santiagocuenta112az-lgtm/glamrock-freddy/mano/mano.stl

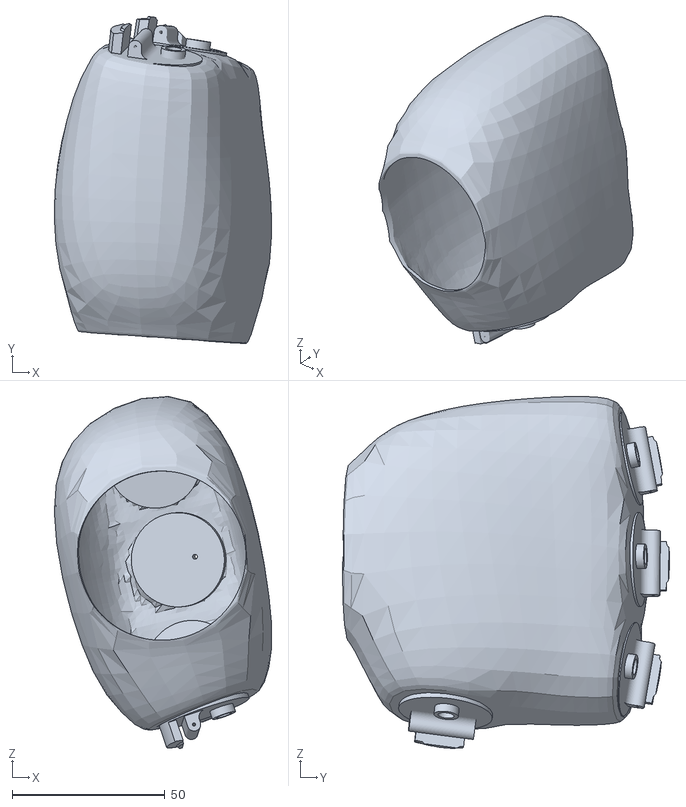
[picture p15: CAD file, 2026-02-24]
mano/mano.stl
71.1 x 107.0 x 115.2
