santiagocuenta112az-lgtm/glamrock-freddy/mis mecanismos/brazo/planetas.stl

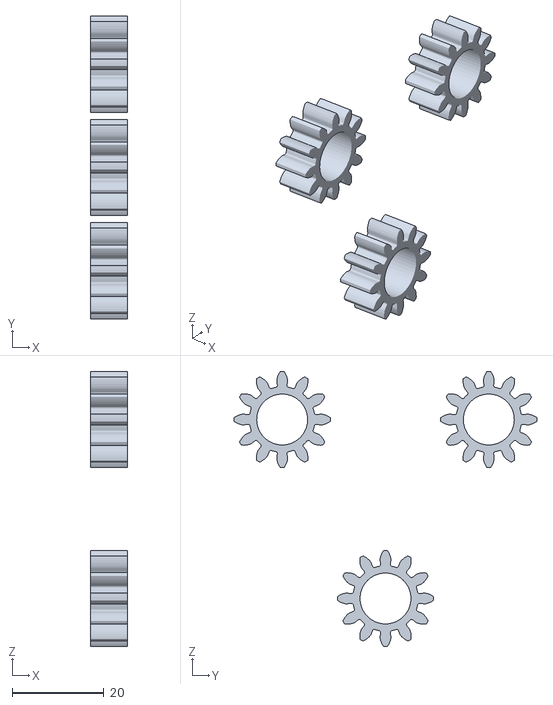
[picture p16: CAD file, 2026-02-24]
mis mecanismos/brazo/planetas.stl
8.00 x 66.0 x 60.0
