santiagocuenta112az-lgtm/glamrock-freddy/mis mecanismos/mecanismo de placa alta/3.stl

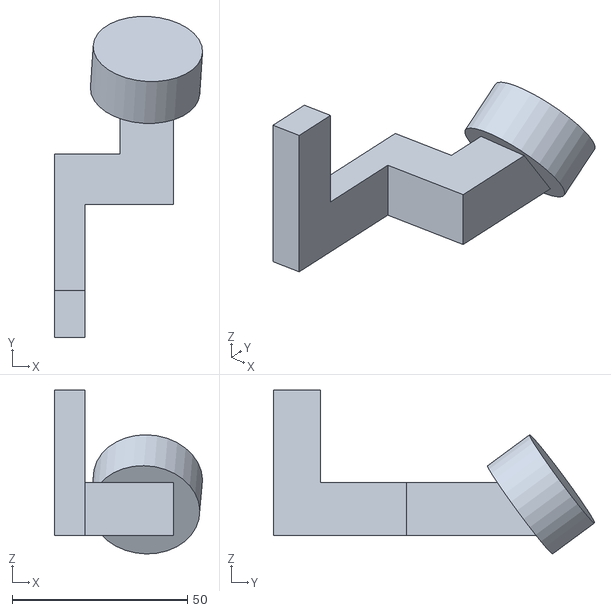
[picture p17: CAD file, 2026-02-24]
mis mecanismos/mecanismo de placa alta/3.stl
42.3 x 91.7 x 46.8
