santiagocuenta112az-lgtm/glamrock-freddy/mis mecanismos/mecanismo giro pecho/2.stl

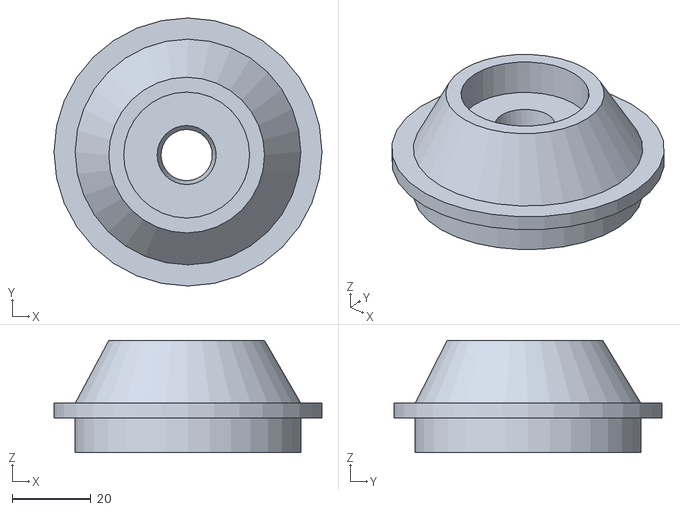
[picture p18: CAD file, 2026-02-24]
mis mecanismos/mecanismo giro pecho/2.stl
68.1 x 68.1 x 28.5
