santiagocuenta112az-lgtm/glamrock-freddy/mis mecanismos/mecanismo placa baja/base del motor.stl

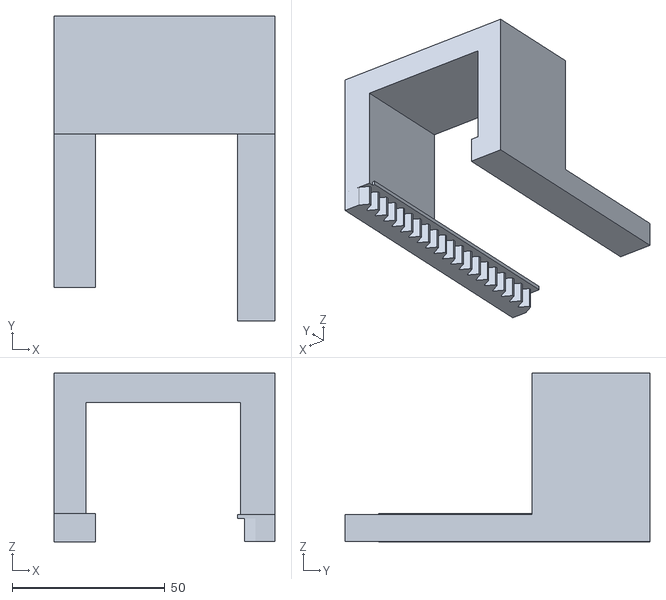
[picture p19: CAD file, 2026-06-25]
mis mecanismos/mecanismo placa baja/base del motor.stl
72.4 x 99.8 x 55.2
