santiagocuenta112az-lgtm/glamrock-freddy/mis mecanismos/soportes/conexioncuellocabeza.stl

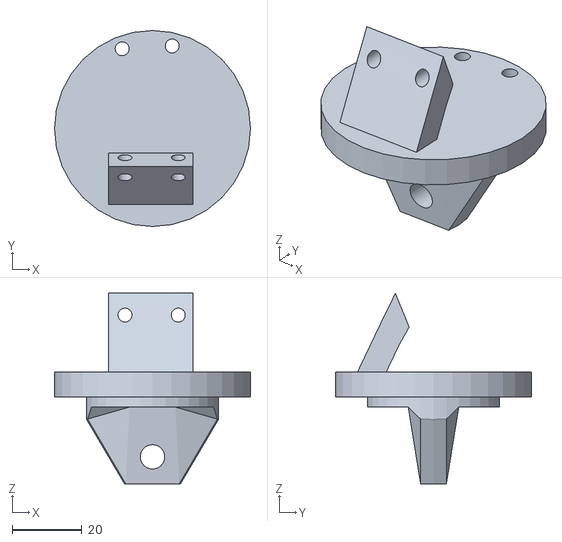
[picture p20: CAD file, 2026-02-24]
mis mecanismos/soportes/conexioncuellocabeza.stl
56.3 x 56.3 x 54.8
