santiagocuenta112az-lgtm/glamrock-freddy/ojos/pestaña.stl

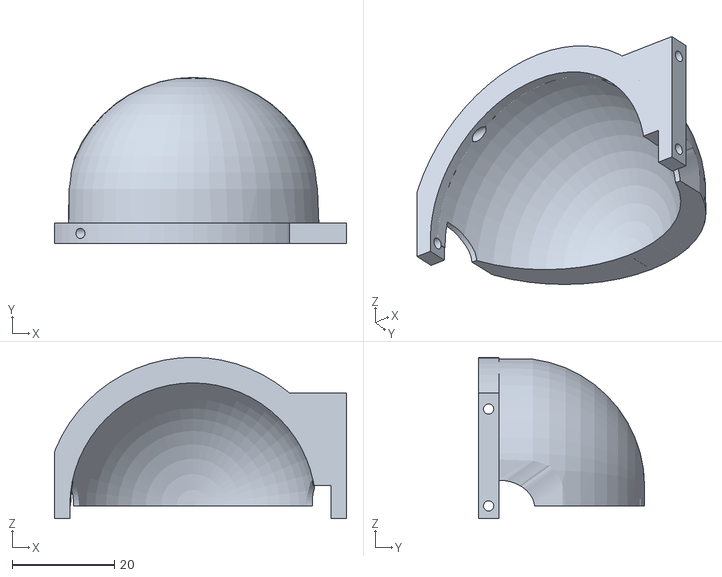
[picture p21: CAD file, 2026-02-24]
ojos/pestaña.stl
57.0 x 32.4 x 31.5
