santiagocuenta112az-lgtm/glamrock-freddy/planetary gearbox.3mf

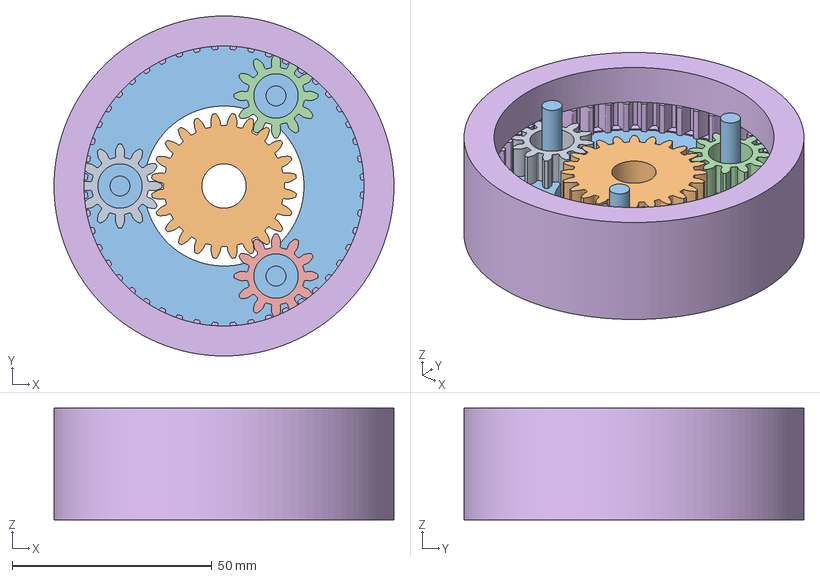
[picture p22: CAD file, 2026-02-24]
planetary gearbox.3mf
85.0 x 85.0 x 28.0 mm
Cuerpo1 x 3
Cuerpo2
Cuerpo3
Cuerpo5
