santiagocuenta112az-lgtm/glamrock-freddy/cara/oreja 2.stl

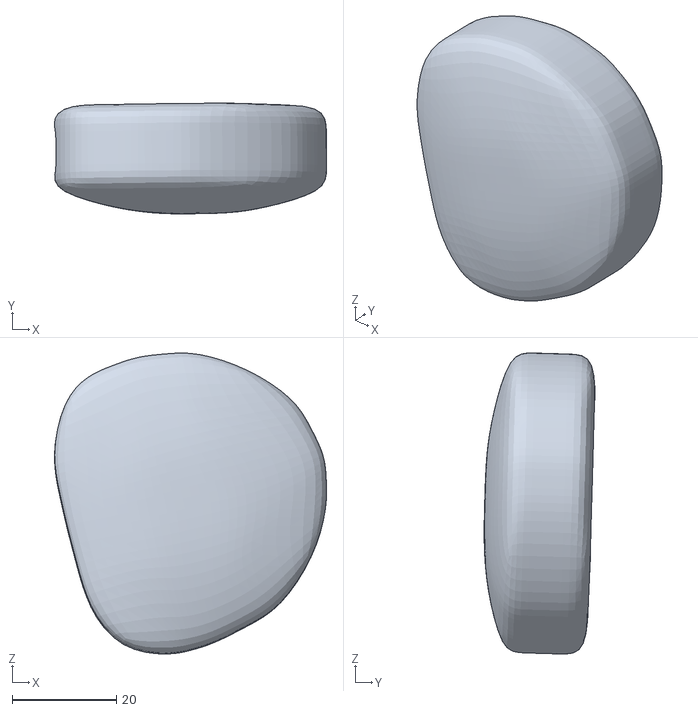
[picture p23: CAD file, 2026-02-24]
cara/oreja 2.stl
52.1 x 21.2 x 57.7
