santiagocuenta112az-lgtm/glamrock-freddy/cuerpo/extremidades/brazo.stl

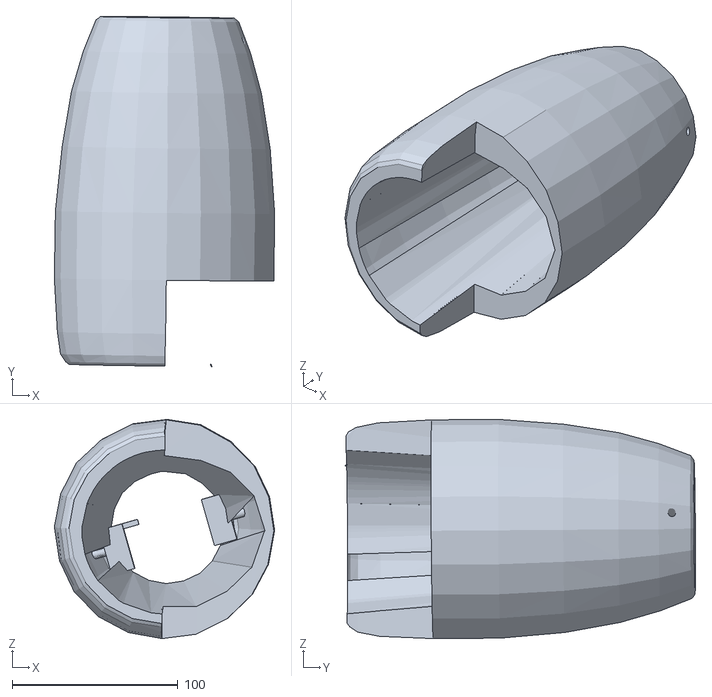
[picture p24: CAD file, 2026-02-24]
cuerpo/extremidades/brazo.stl
132.9 x 211.2 x 132.2
