santiagocuenta112az-lgtm/glamrock-freddy/cuerpo/palcaup.stl

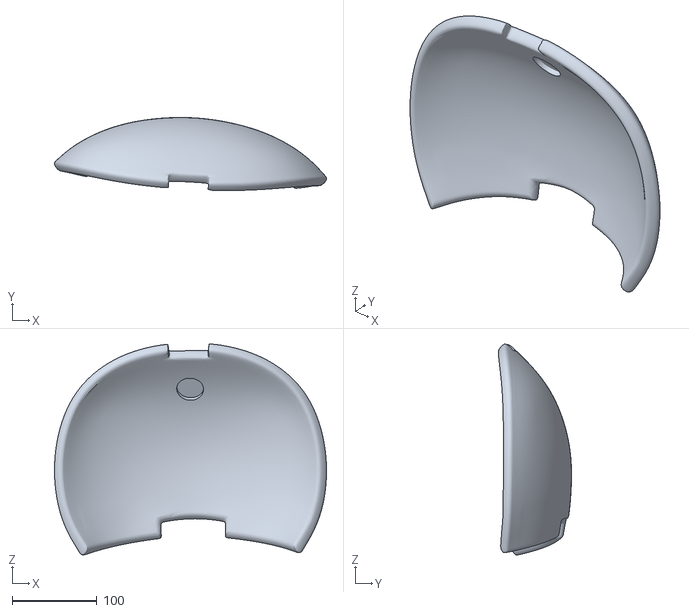
[picture p25: CAD file, 2026-02-24]
cuerpo/palcaup.stl
320.1 x 86.0 x 248.2
