santiagocuenta112az-lgtm/glamrock-freddy/mano/dedomid.stl

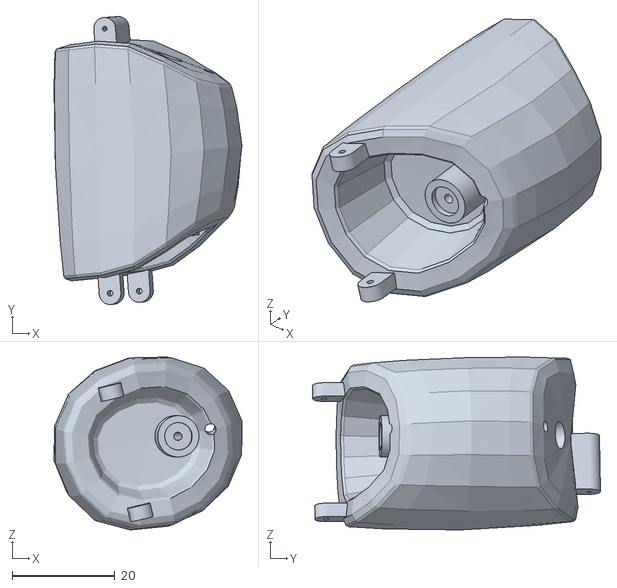
[picture p26: CAD file, 2026-02-24]
mano/dedomid.stl
36.5 x 55.9 x 33.6
