santiagocuenta112az-lgtm/glamrock-freddy/mis mecanismos/brazo/portaplanetas.stl

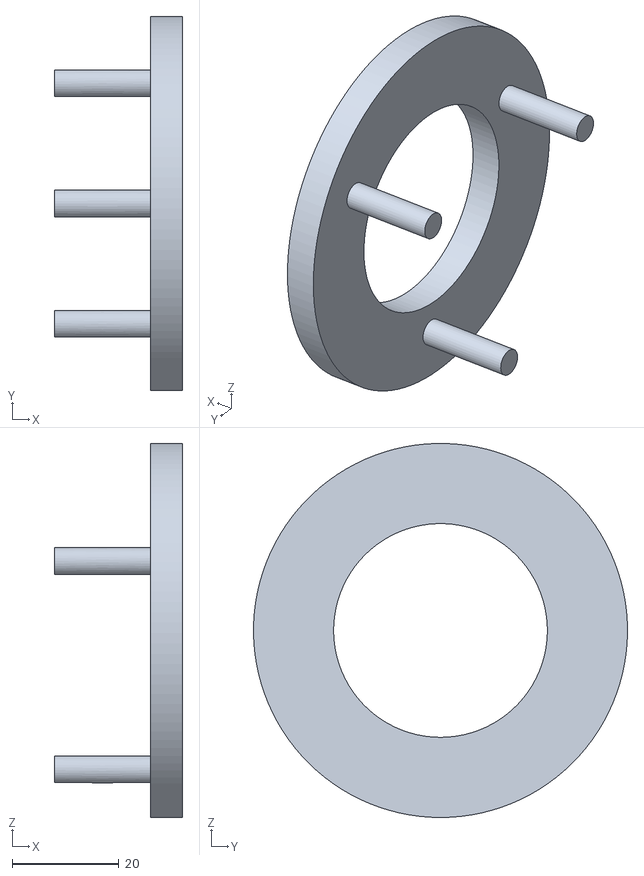
[picture p27: CAD file, 2026-02-24]
mis mecanismos/brazo/portaplanetas.stl
24.0 x 70.0 x 70.0
