santiagocuenta112az-lgtm/glamrock-freddy/mis mecanismos/mecanismo de placa alta/engranaje.stl

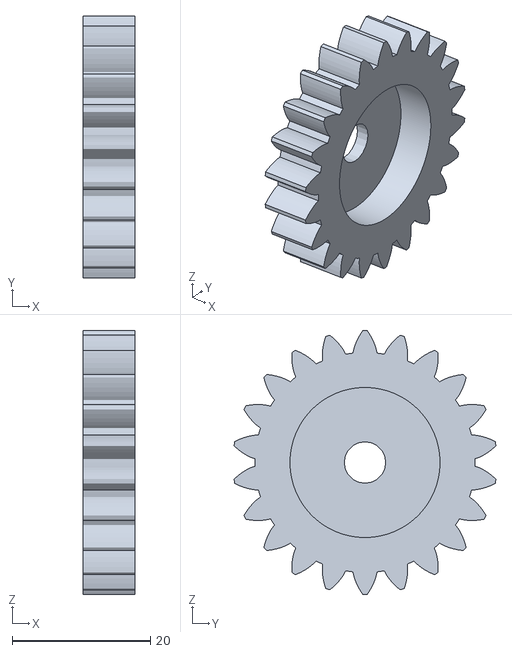
[picture p28: CAD file, 2026-02-24]
mis mecanismos/mecanismo de placa alta/engranaje.stl
7.50 x 37.9 x 38.2
