santiagocuenta112az-lgtm/glamrock-freddy/mis mecanismos/mecanismo giro pecho/1.stl

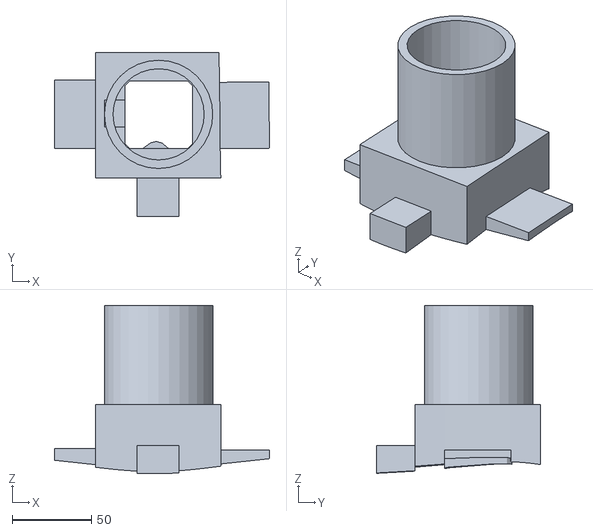
[picture p29: CAD file, 2026-02-24]
mis mecanismos/mecanismo giro pecho/1.stl
135.8 x 103.3 x 106.4
