santiagocuenta112az-lgtm/glamrock-freddy/mis mecanismos/mecanismo placa baja/1.stl

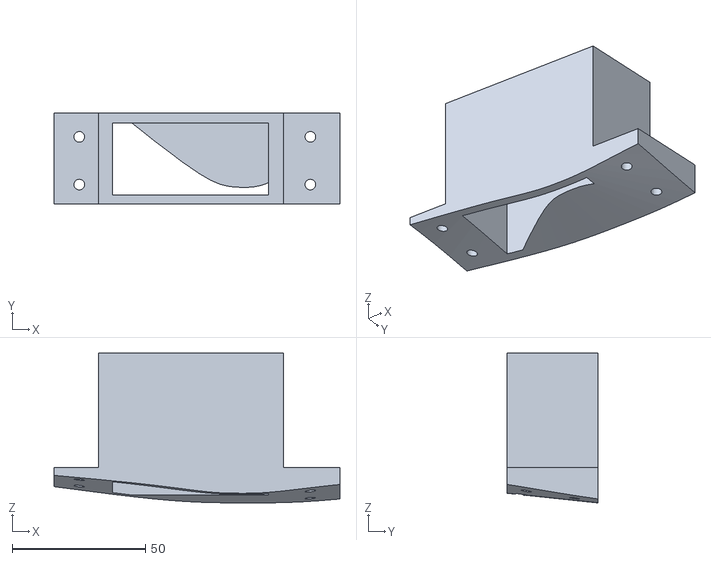
[picture p30: CAD file, 2026-02-24]
mis mecanismos/mecanismo placa baja/1.stl
107.2 x 34.2 x 56.2
