santiagocuenta112az-lgtm/glamrock-freddy/mis mecanismos/soportes/cabeza.stl

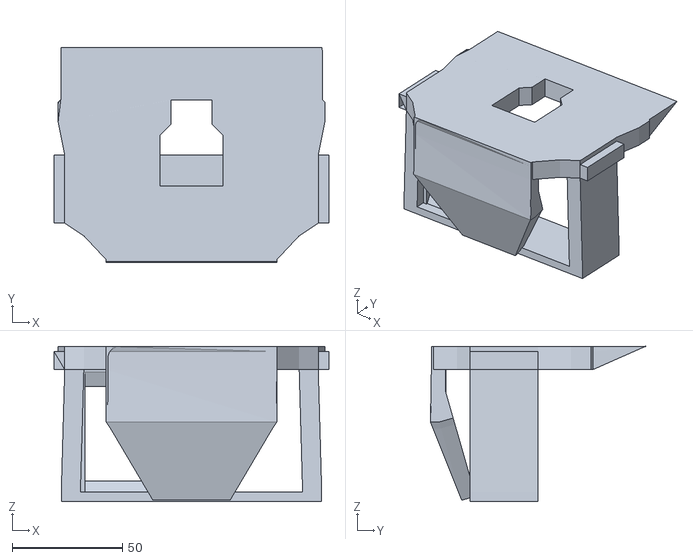
[picture p31: CAD file, 2026-02-24]
mis mecanismos/soportes/cabeza.stl
124.9 x 97.8 x 70.6
