santiagocuenta112az-lgtm/glamrock-freddy/ojos/coenxionojomecanismo.stl

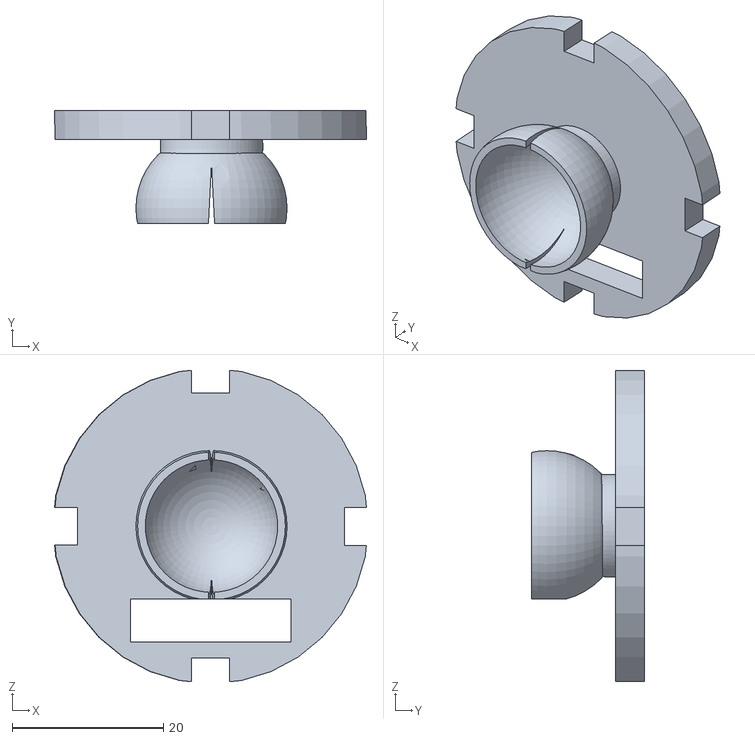
[picture p32: CAD file, 2026-02-24]
ojos/coenxionojomecanismo.stl
41.3 x 14.9 x 41.2
