santiagocuenta112az-lgtm/glamrock-freddy/cara/midface.stl

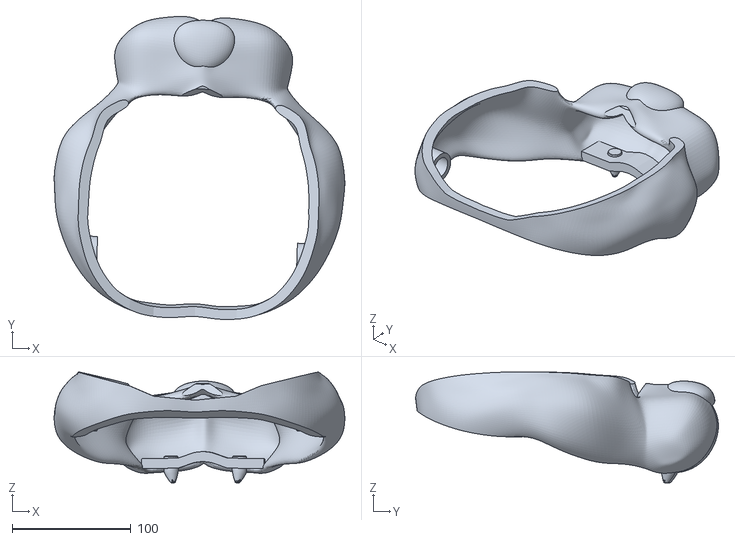
[picture p33: CAD file, 2026-02-24]
cara/midface.stl
244.7 x 255.1 x 93.4
