santiagocuenta112az-lgtm/glamrock-freddy/cuerpo/extremidades/antebtrazo.stl

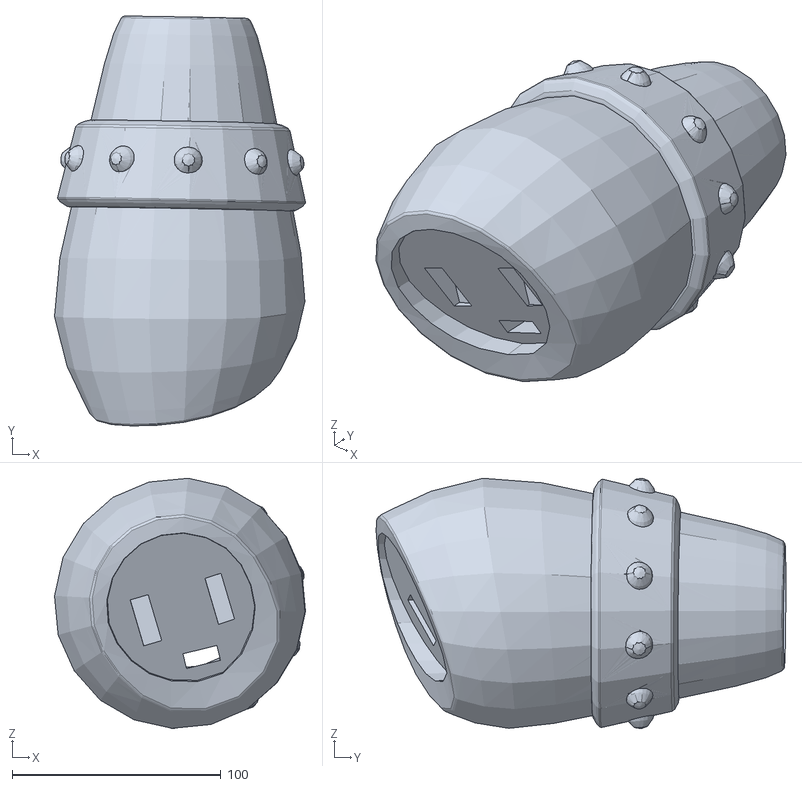
[picture p34: CAD file, 2026-02-24]
cuerpo/extremidades/antebtrazo.stl
120.3 x 196.5 x 120.1
