santiagocuenta112az-lgtm/glamrock-freddy/cuerpo/pecho.stl

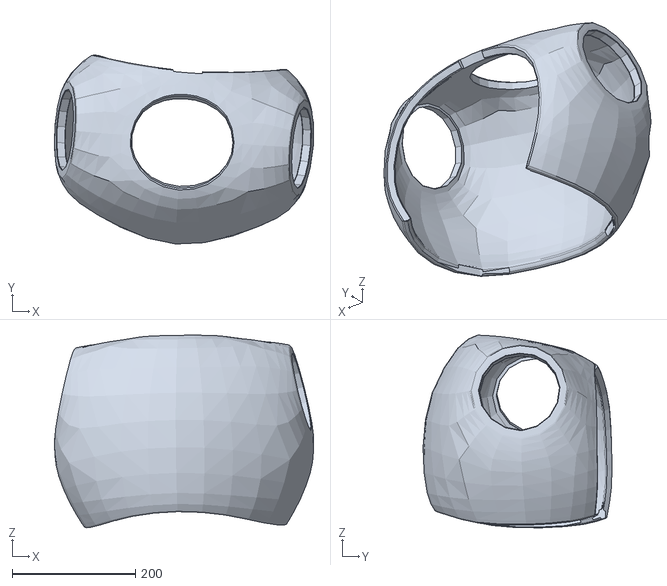
[picture p35: CAD file, 2026-02-24]
cuerpo/pecho.stl
420.2 x 306.6 x 312.5
