santiagocuenta112az-lgtm/glamrock-freddy/mis mecanismos/brazo/conexionsoporteservo.stl

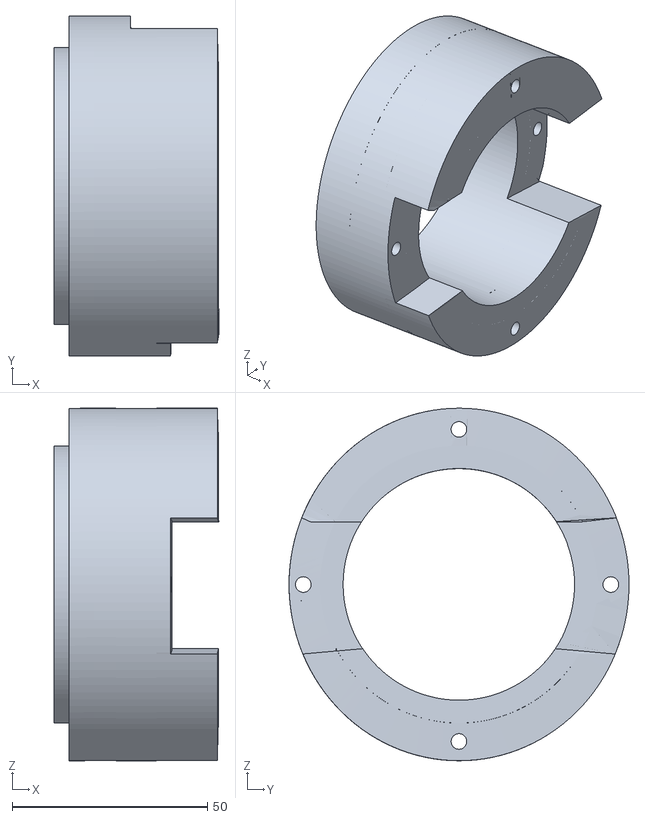
[picture p36: CAD file, 2026-02-24]
mis mecanismos/brazo/conexionsoporteservo.stl
42.2 x 87.0 x 90.3
