santiagocuenta112az-lgtm/glamrock-freddy/mis mecanismos/mecanismo de placa alta/2.stl

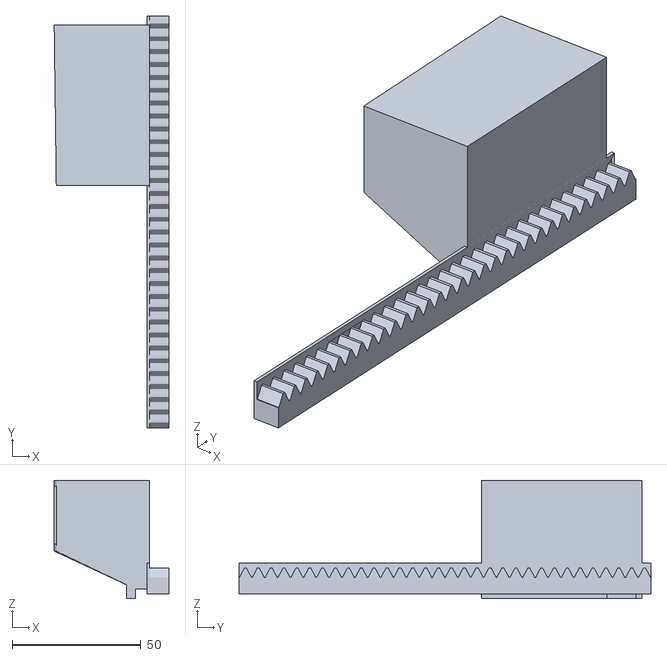
[picture p37: CAD file, 2026-02-24]
mis mecanismos/mecanismo de placa alta/2.stl
44.5 x 160.1 x 45.9
