santiagocuenta112az-lgtm/glamrock-freddy/mis mecanismos/soportes/1p.stl

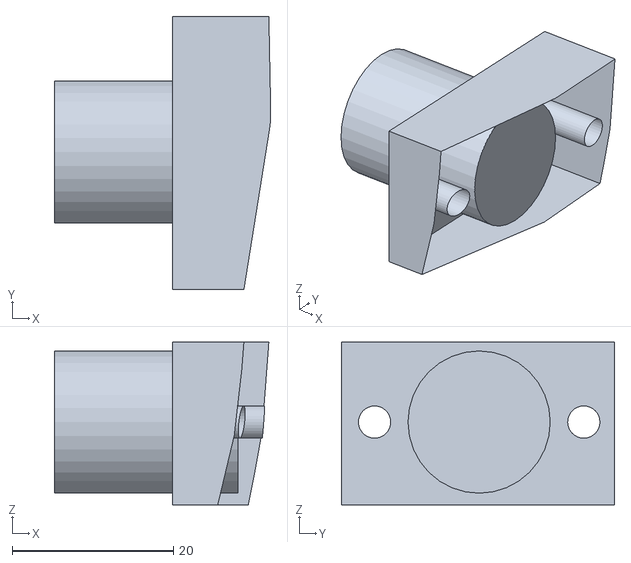
[picture p38: CAD file, 2026-02-24]
mis mecanismos/soportes/1p.stl
26.8 x 33.9 x 20.2
