santiagocuenta112az-lgtm/glamrock-freddy/ojos/ojo.stl

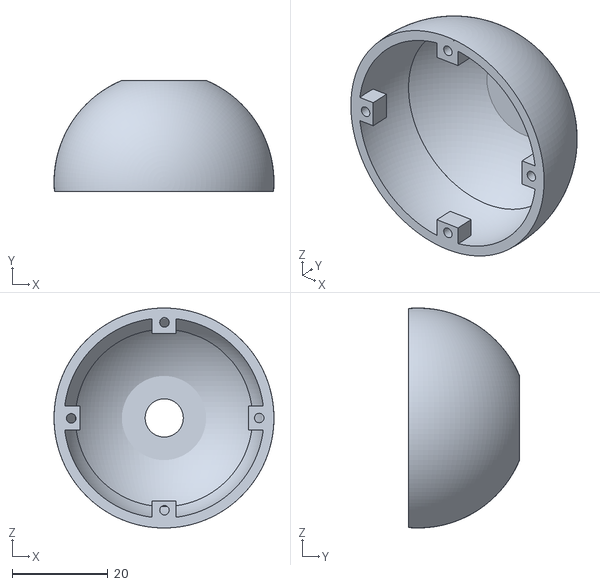
[picture p39: CAD file, 2026-02-24]
ojos/ojo.stl
46.0 x 23.2 x 46.0
