santiagocuenta112az-lgtm/glamrock-freddy/cara/mandibula.stl

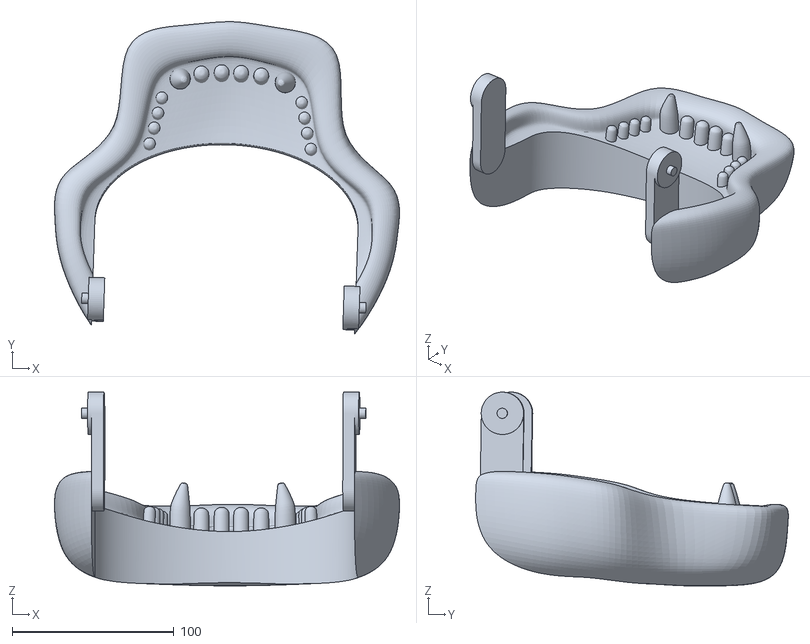
[picture p40: CAD file, 2026-02-24]
cara/mandibula.stl
213.4 x 193.4 x 119.9
