santiagocuenta112az-lgtm/glamrock-freddy/cuerpo/extremidades/pie.stl

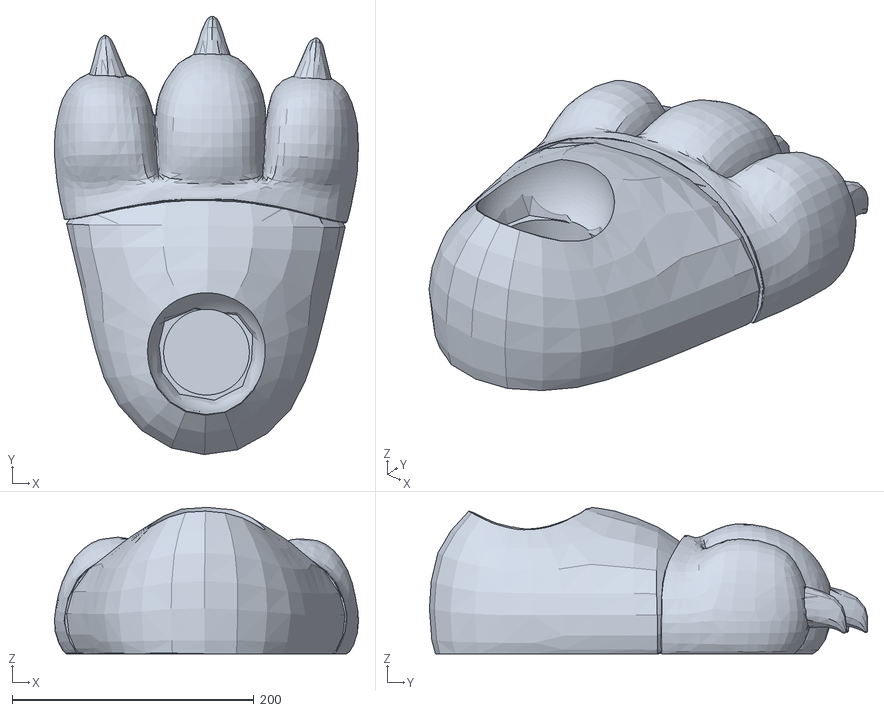
[picture p41: CAD file, 2026-02-24]
cuerpo/extremidades/pie.stl
251.4 x 362.4 x 121.2
