santiagocuenta112az-lgtm/glamrock-freddy/cuerpo/placadown.stl

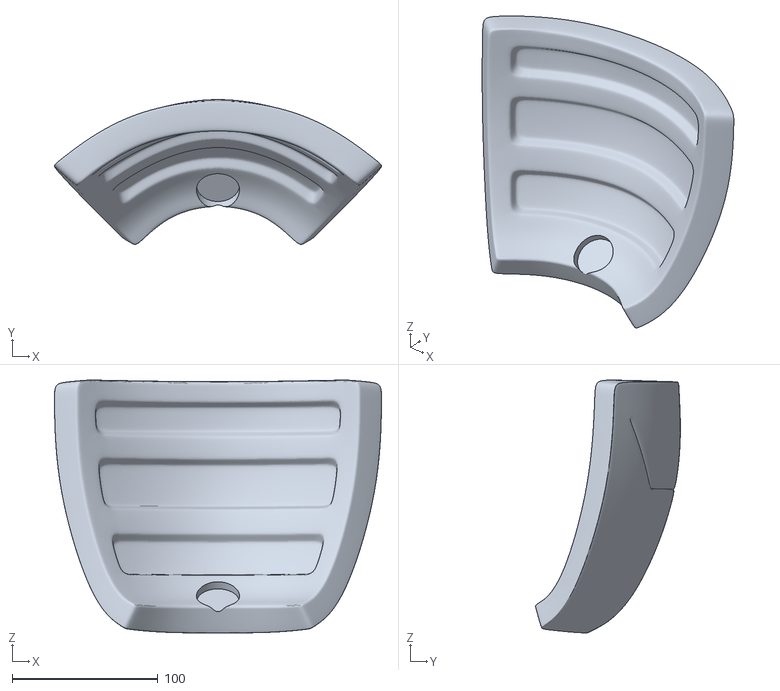
[picture p42: CAD file, 2026-02-24]
cuerpo/placadown.stl
224.4 x 99.4 x 173.6
