santiagocuenta112az-lgtm/glamrock-freddy/mis mecanismos/brazo/soporte servo.stl

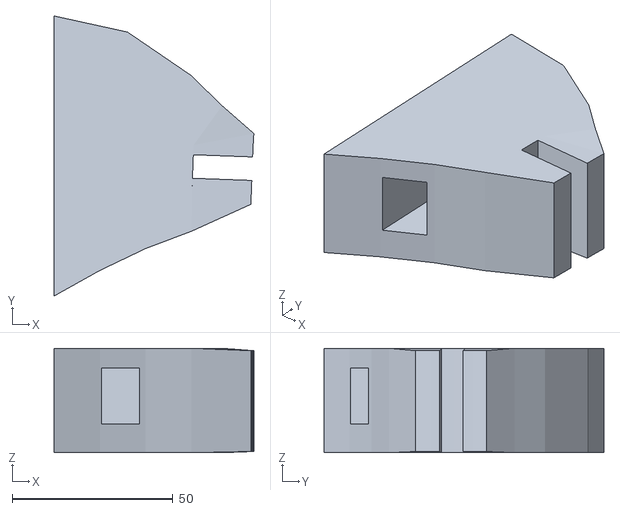
[picture p43: CAD file, 2026-02-24]
mis mecanismos/brazo/soporte servo.stl
62.1 x 87.1 x 32.5
