santiagocuenta112az-lgtm/glamrock-freddy/mis mecanismos/soportes/3c.stl

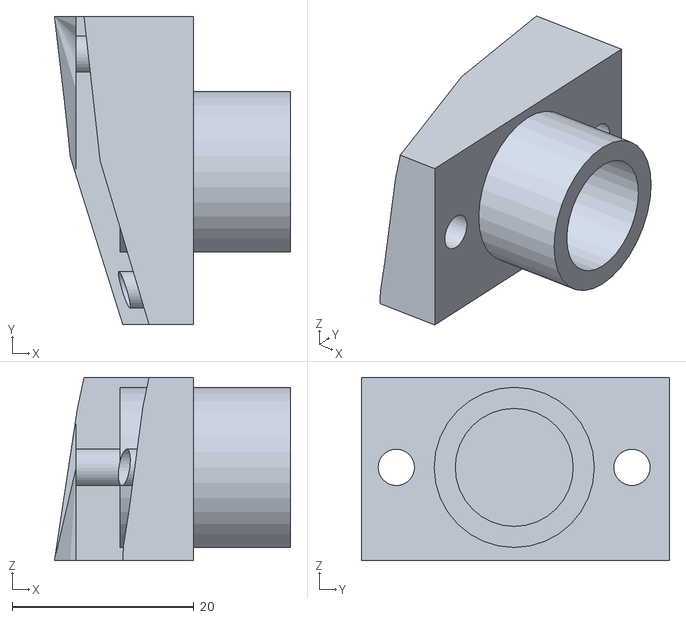
[picture p44: CAD file, 2026-02-24]
mis mecanismos/soportes/3c.stl
26.0 x 33.9 x 20.2
