santiagocuenta112az-lgtm/glamrock-freddy/cuerpo/abdomen.stl

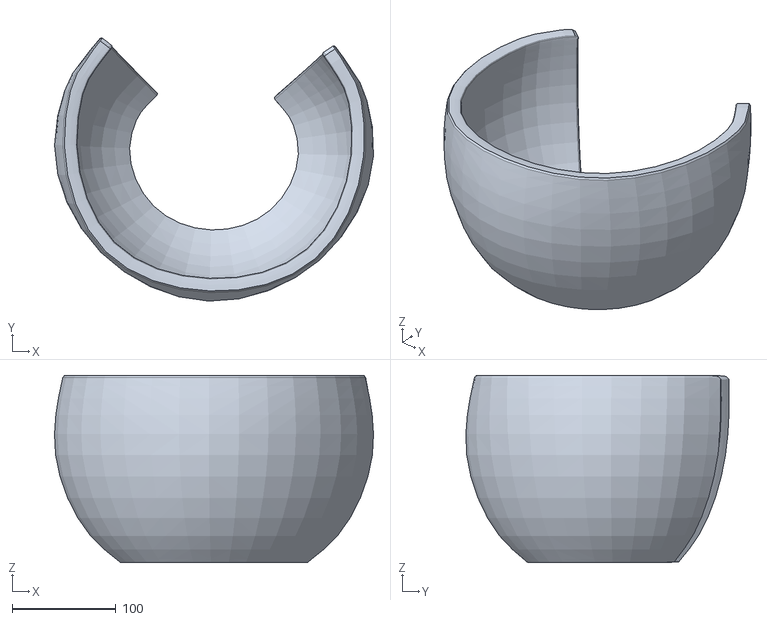
[picture p45: CAD file, 2026-02-24]
cuerpo/abdomen.stl
307.1 x 253.5 x 180.2
