santiagocuenta112az-lgtm/glamrock-freddy/mis mecanismos/brazo/sol.stl

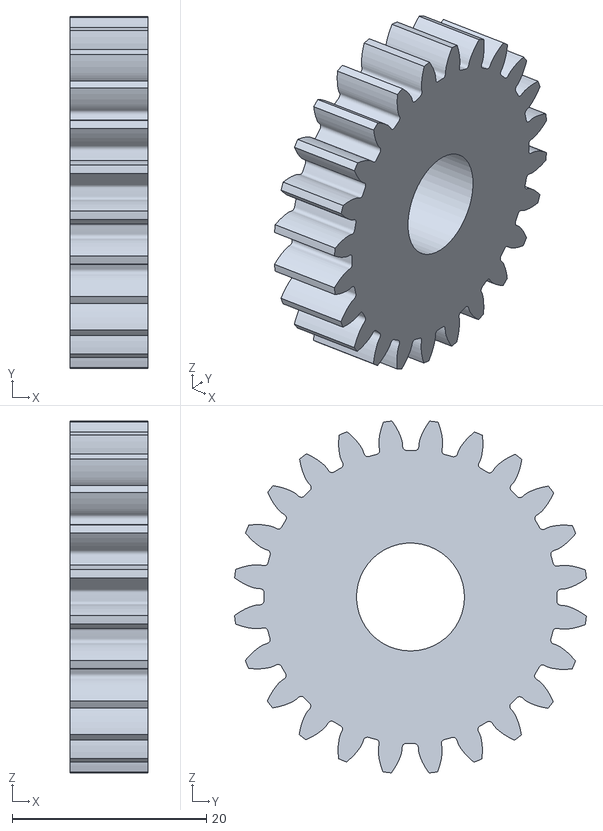
[picture p46: CAD file, 2026-02-24]
mis mecanismos/brazo/sol.stl
8.00 x 36.2 x 36.2
