santiagocuenta112az-lgtm/glamrock-freddy/mis mecanismos/mecanismo placa baja/3.stl

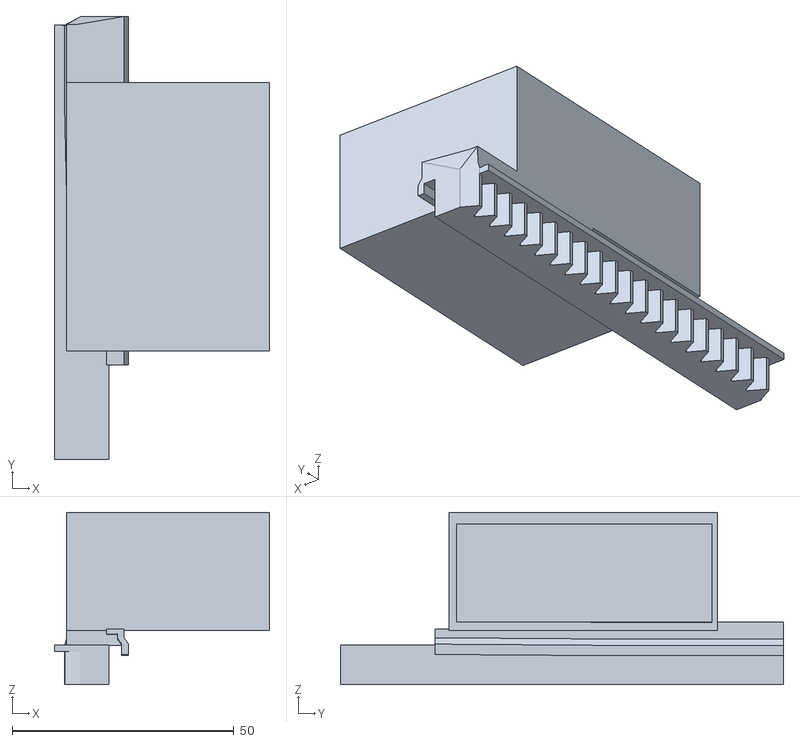
[picture p47: CAD file, 2026-02-24]
mis mecanismos/mecanismo placa baja/3.stl
48.5 x 99.8 x 38.8
