santiagocuenta112az-lgtm/glamrock-freddy/mis mecanismos/soportes/soporte sensor.stl

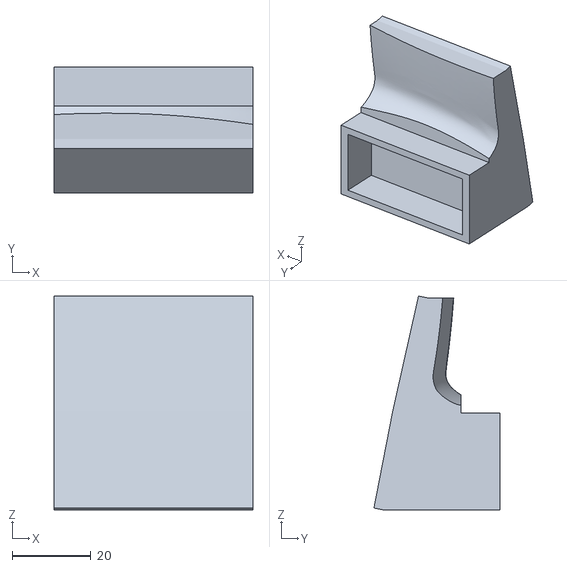
[picture p48: CAD file, 2026-02-24]
mis mecanismos/soportes/soporte sensor.stl
50.4 x 32.0 x 54.2
