santiagocuenta112az-lgtm/glamrock-freddy/cuerpo/pelvis.stl

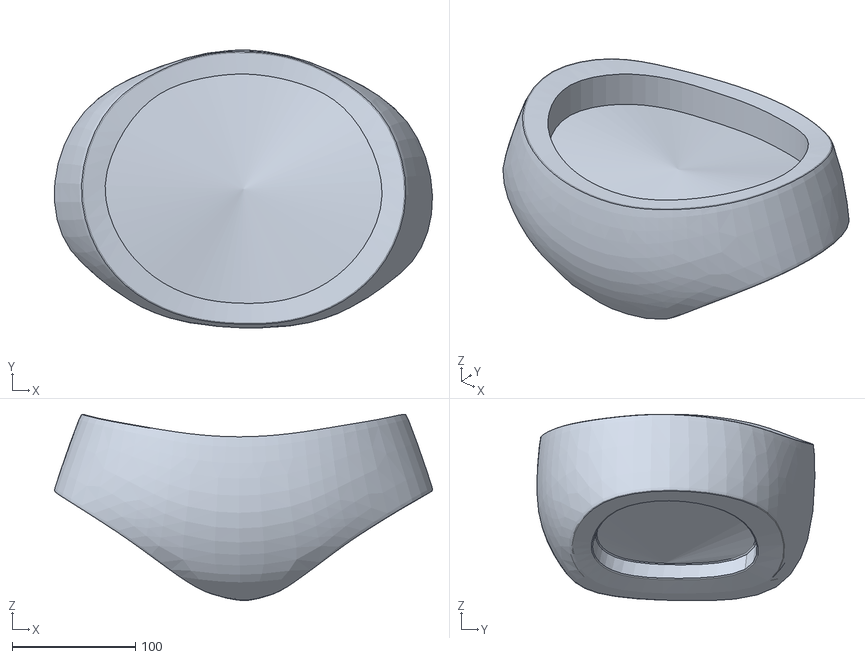
[picture p49: CAD file, 2026-02-24]
cuerpo/pelvis.stl
307.1 x 225.7 x 151.4
