santiagocuenta112az-lgtm/glamrock-freddy/mis mecanismos/brazo/soporte brazo.stl

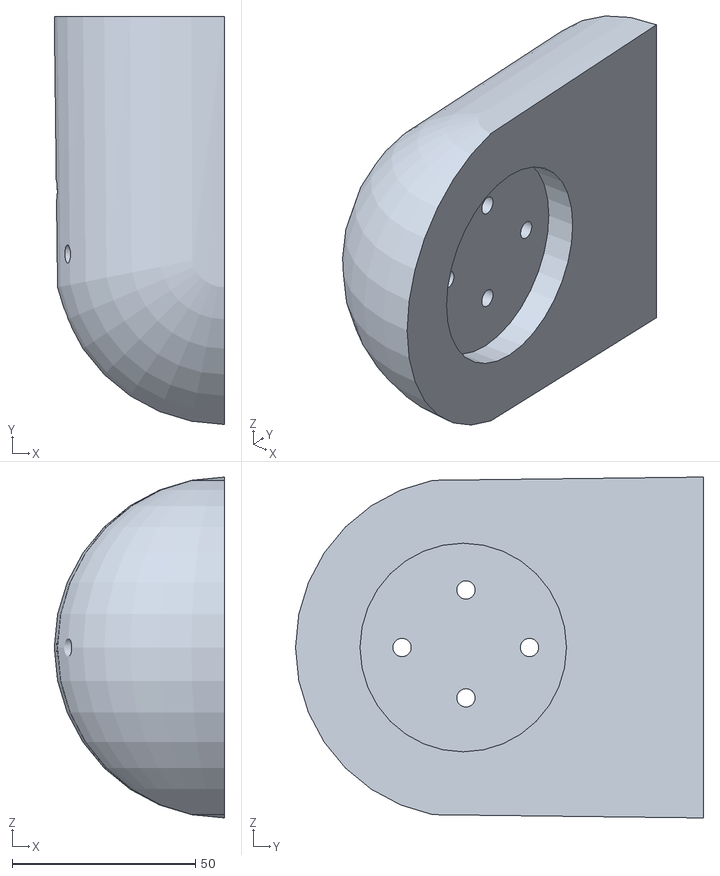
[picture p50: CAD file, 2026-02-24]
mis mecanismos/brazo/soporte brazo.stl
46.5 x 111.3 x 93.0
