santiagocuenta112az-lgtm/glamrock-freddy/mis mecanismos/soportes/1c.stl

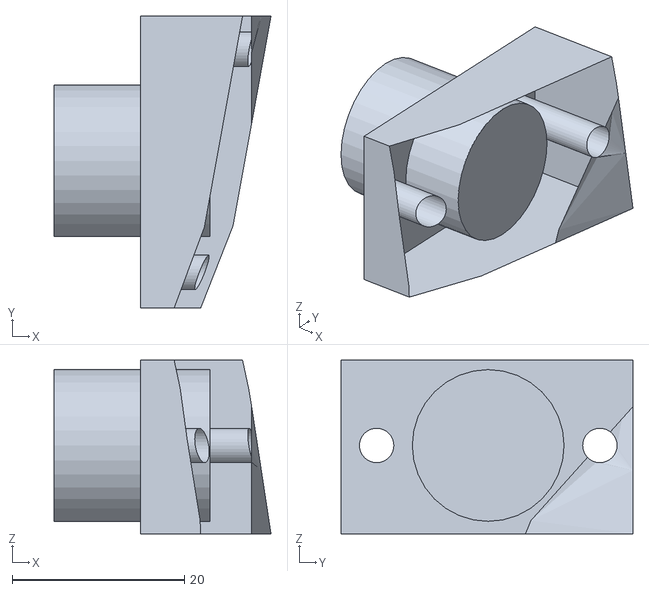
[picture p51: CAD file, 2026-02-24]
mis mecanismos/soportes/1c.stl
25.2 x 33.9 x 20.2
