santiagocuenta112az-lgtm/glamrock-freddy/mis mecanismos/brazo/salidadetorque.stl

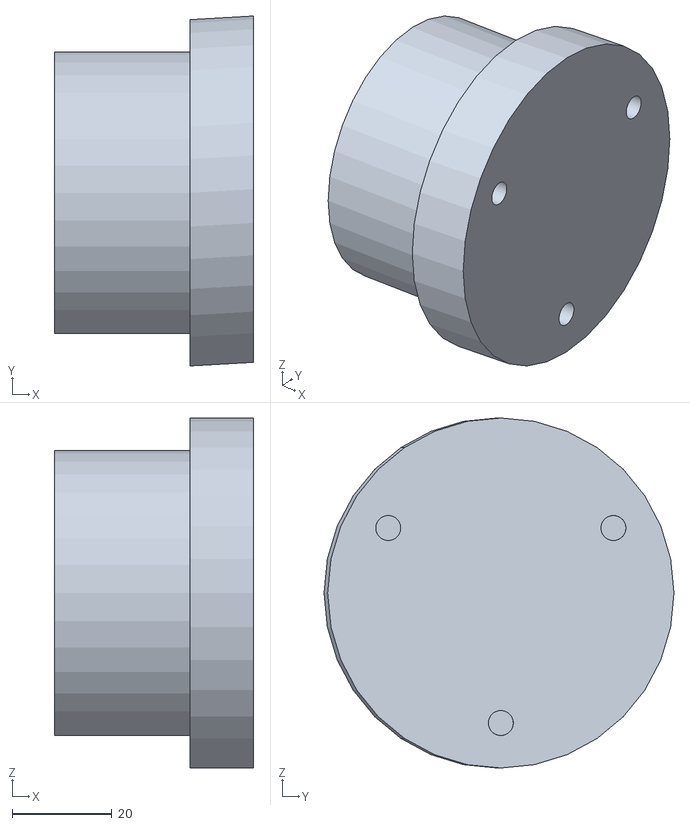
[picture p52: CAD file, 2026-02-24]
mis mecanismos/brazo/salidadetorque.stl
39.8 x 70.0 x 70.0
