santiagocuenta112az-lgtm/glamrock-freddy/mis mecanismos/soportes/2c.stl

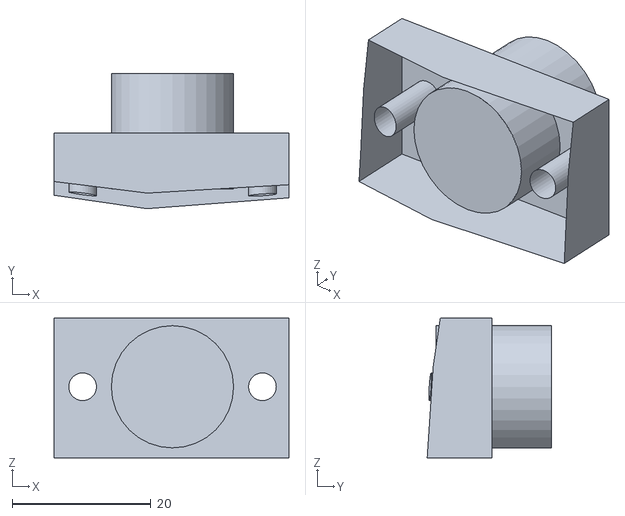
[picture p53: CAD file, 2026-02-24]
mis mecanismos/soportes/2c.stl
33.9 x 19.5 x 20.2
