santiagocuenta112az-lgtm/glamrock-freddy/mis mecanismos/brazo/corona.stl

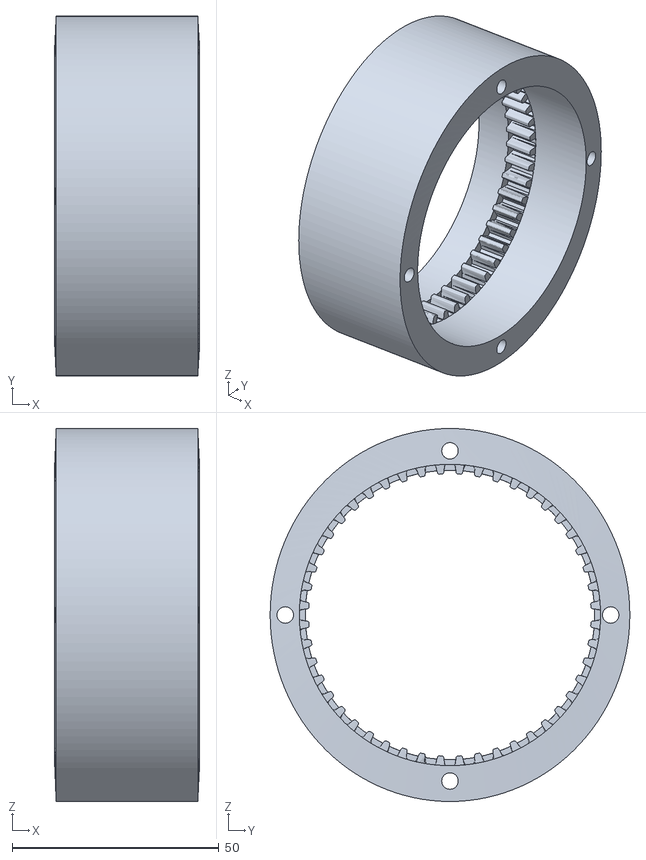
[picture p54: CAD file, 2026-02-24]
mis mecanismos/brazo/corona.stl
35.1 x 87.0 x 90.2
