santiagocuenta112az-lgtm/glamrock-freddy/mis mecanismos/soportes/movimiento cuello.stl

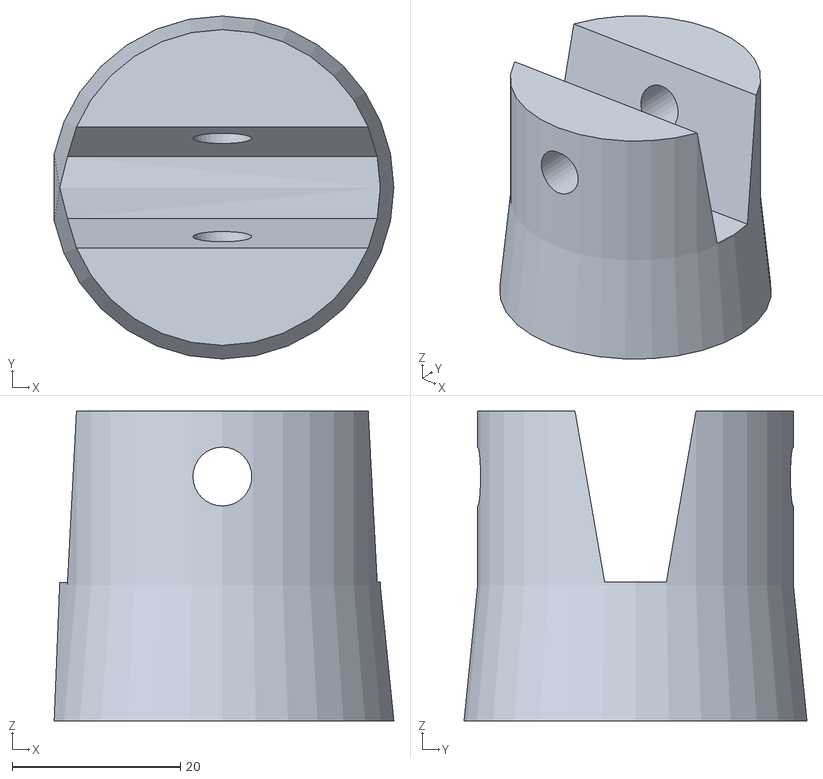
[picture p55: CAD file, 2026-02-24]
mis mecanismos/soportes/movimiento cuello.stl
40.4 x 40.8 x 36.8
