santiagocuenta112az-lgtm/glamrock-freddy/mis mecanismos/soportes/soporte de cuello.stl

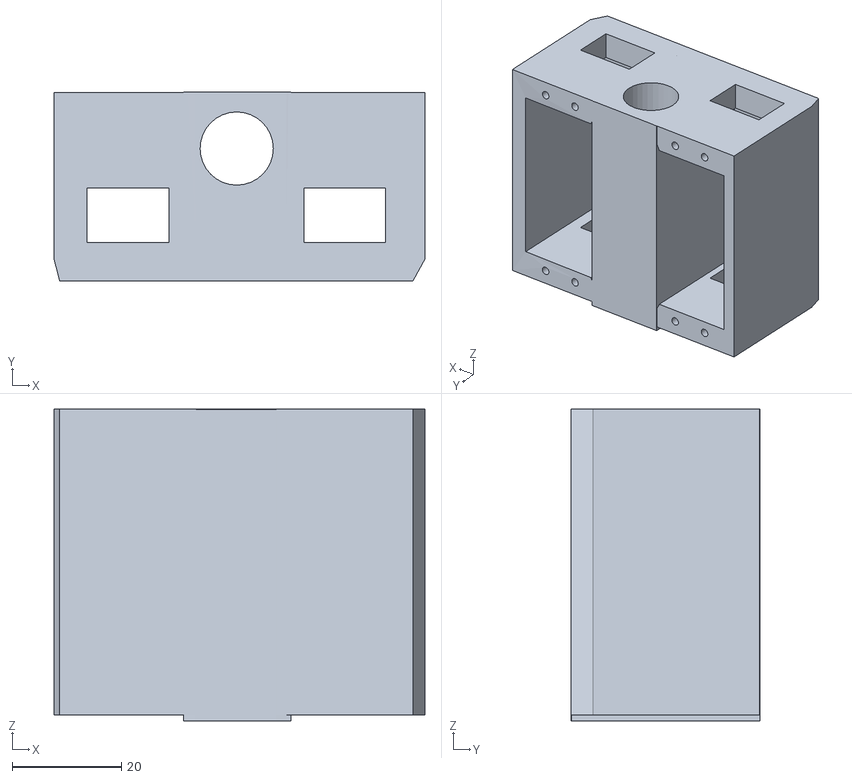
[picture p56: CAD file, 2026-02-24]
mis mecanismos/soportes/soporte de cuello.stl
67.9 x 34.6 x 57.1
