santiagocuenta112az-lgtm/glamrock-freddy/mis mecanismos/soportes/soport2cabeza.stl

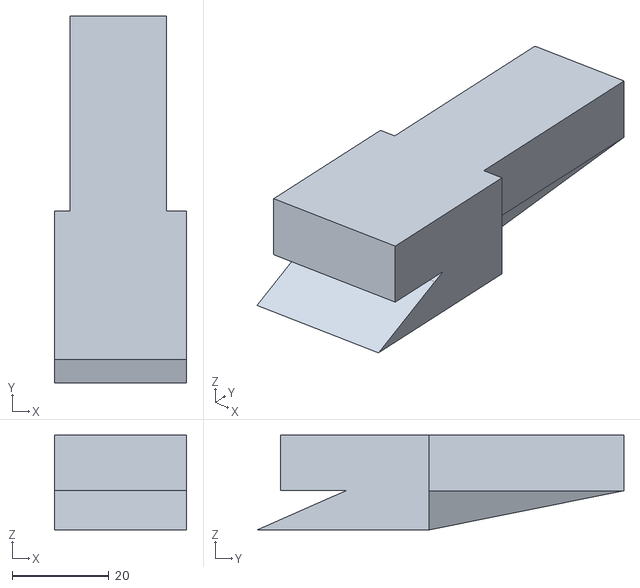
[picture p57: CAD file, 2026-02-24]
mis mecanismos/soportes/soport2cabeza.stl
27.3 x 75.9 x 19.6
