santiagocuenta112az-lgtm/glamrock-freddy/mis mecanismos/soportes/soportecabeza.stl

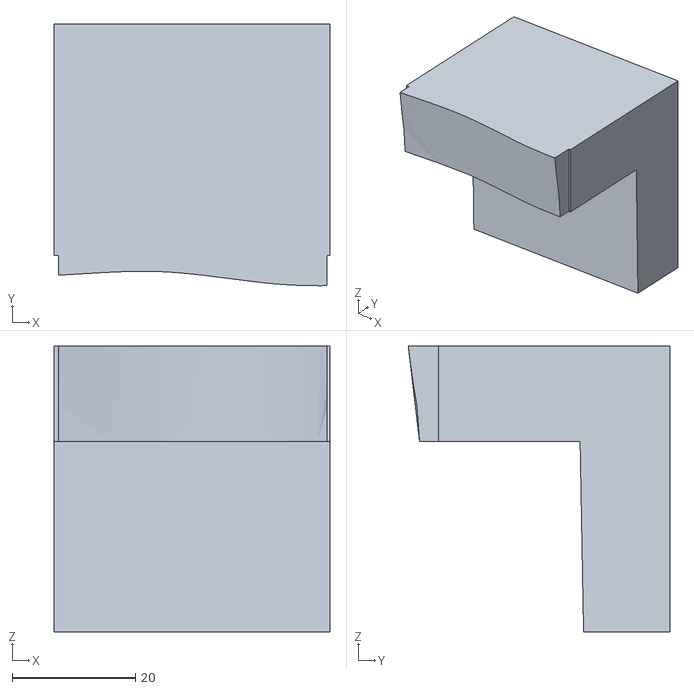
[picture p58: CAD file, 2026-02-24]
mis mecanismos/soportes/soportecabeza.stl
44.8 x 42.5 x 46.4
