santiagocuenta112az-lgtm/glamrock-freddy/mis mecanismos/soportes/2p.stl

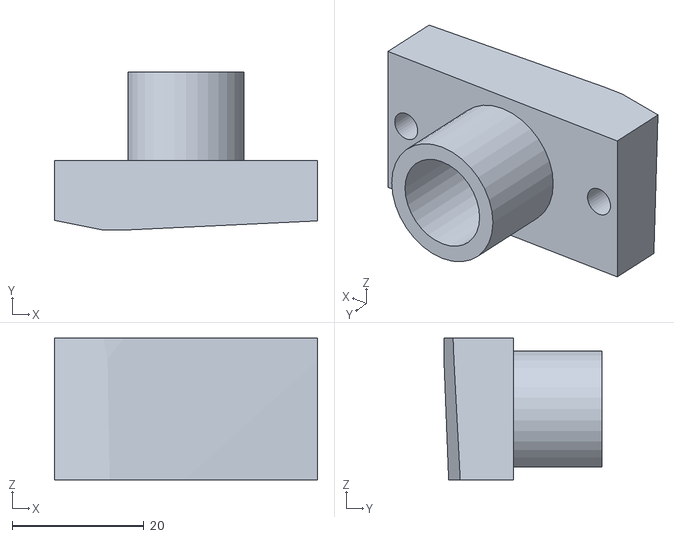
[picture p59: CAD file, 2026-02-24]
mis mecanismos/soportes/2p.stl
40.0 x 24.0 x 21.6
